lidarsee/lidarsee_v2_alpha/InventorCAD/lidarsee/stl/Mount_0.stl

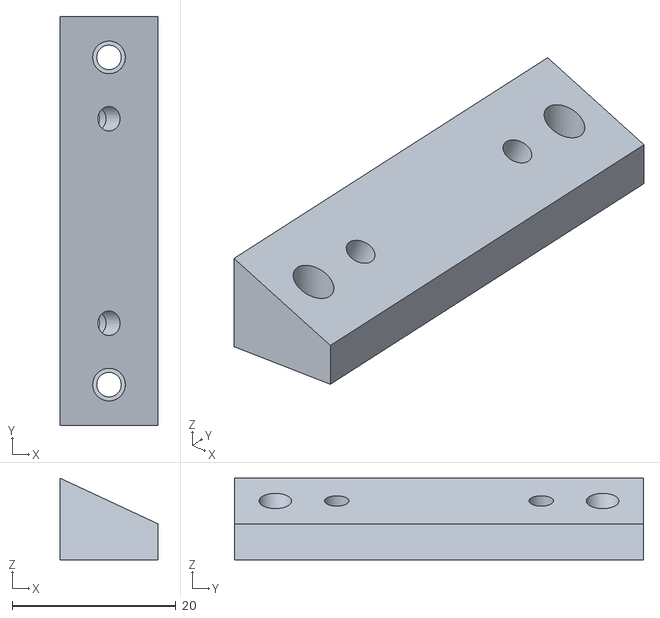
[picture p22: CAD file, 2017-08-03]
InventorCAD/lidarsee/stl/Mount_0.stl
12.0 x 50.0 x 10.0
